thingSoC/TSOC-USBUART1/TSOC-USBUART1/images/TSOC-USBUART1_iso.png

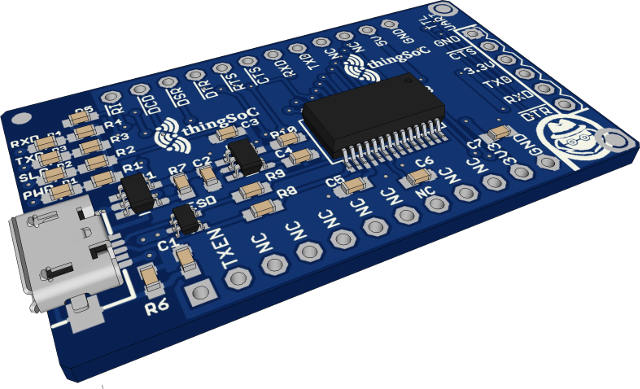
TSOC-USBUART1/images/TSOC-USBUART1_iso.png
